IITA-Proyectos/RoboCupJunior-Soccer-Open-League-2025/Diseño3D/Grand Jaagub-Bigery.stl

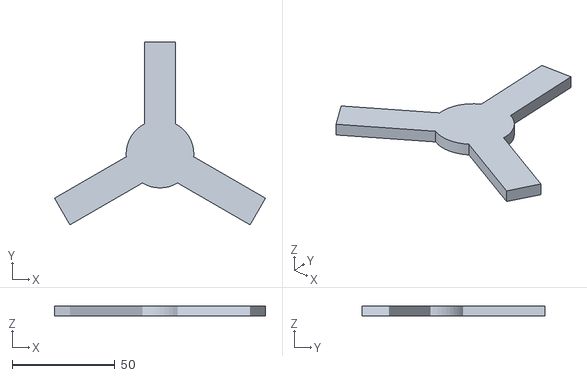
[picture p15: CAD file, 2025-07-25]
Diseño3D/Grand Jaagub-Bigery.stl
102.8 x 89.0 x 5.00
