IITA-Proyectos/RoboCupJunior-Soccer-Open-League-2025/Diseño3D/soporte TT motor_recortado 2025-07-23 - seba.stl

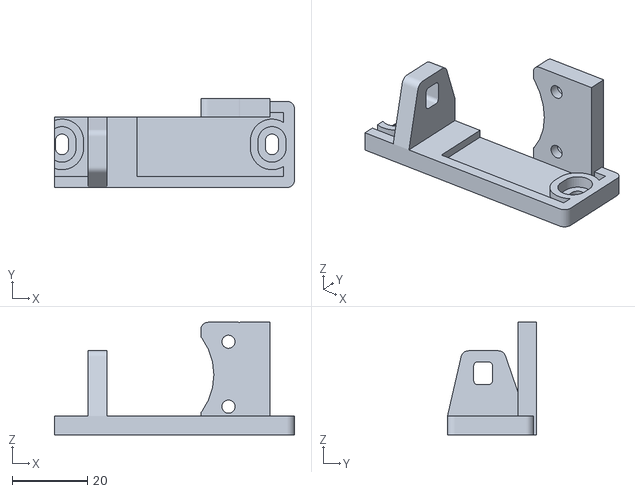
[picture p16: CAD file, 2025-07-24]
Diseño3D/soporte TT motor_recortado 2025-07-23 - seba.stl
64.0 x 23.8 x 30.0
