IITA-Proyectos/RoboCupJunior-Soccer-Open-League-2025/Diseño3D/2.0intentoconalturamijae3l.stl

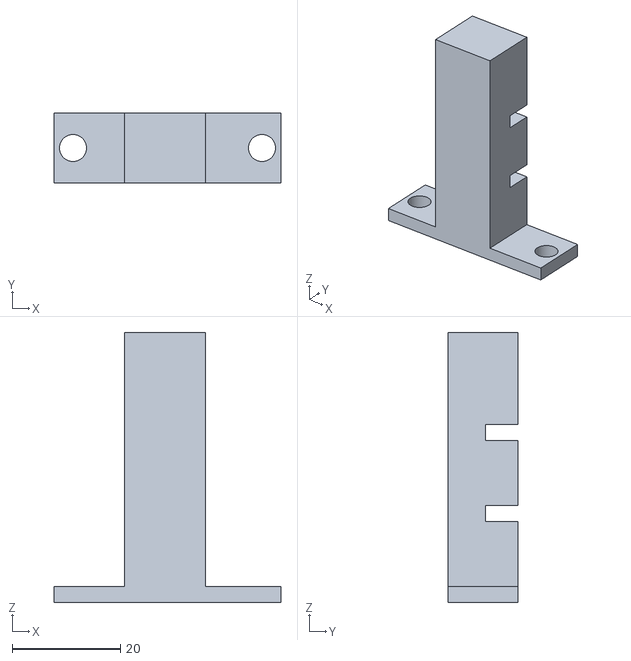
[picture p17: CAD file, 2025-07-22]
Diseño3D/2.0intentoconalturamijae3l.stl
42.0 x 13.0 x 50.0
