IITA-Proyectos/RoboCupJunior-Soccer-Open-League-2025/Diseño3D/mijael.barra.stl

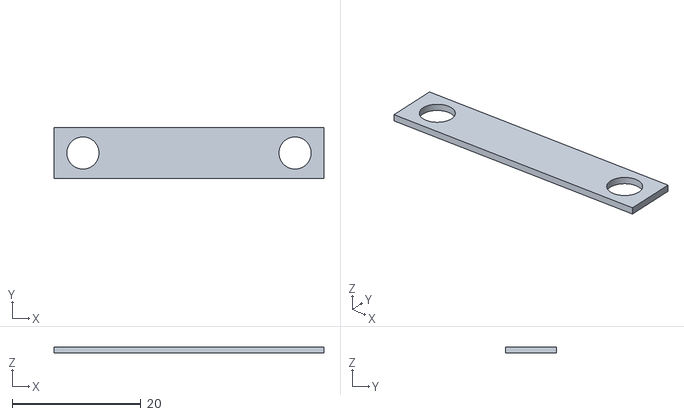
[picture p18: CAD file, 2025-07-22]
Diseño3D/mijael.barra.stl
42.0 x 8.00 x 1.00
