IITA-Proyectos/RoboCupJunior-Soccer-Open-League-2025/Diseño3D/Fabulous Lappi.stl

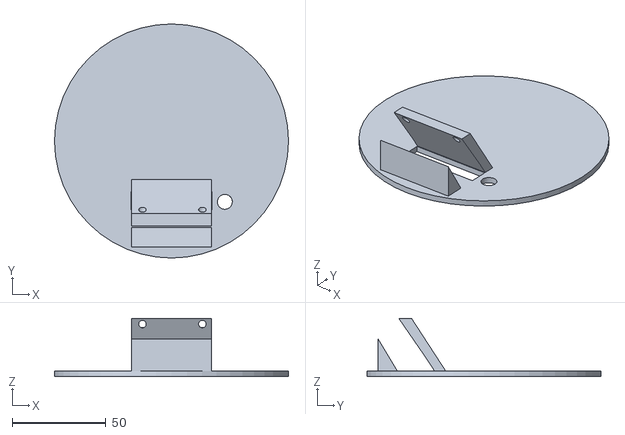
[picture p19: CAD file, 2025-07-22]
Diseño3D/Fabulous Lappi.stl
125.0 x 125.0 x 31.0
