IITA-Proyectos/RoboCupJunior-Soccer-Open-League-2025/Diseño3D/base-0.3demijael.stl

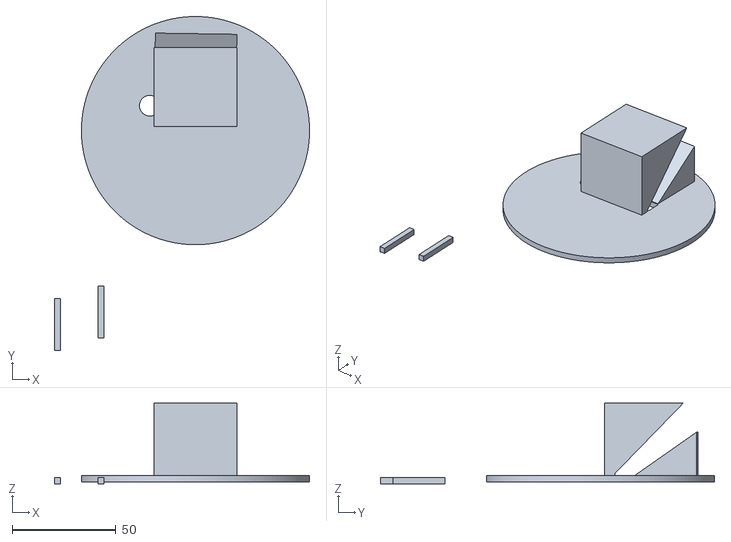
[picture p20: CAD file, 2025-07-01]
Diseño3D/base-0.3demijael.stl
123.0 x 161.0 x 39.0
