IITA-Proyectos/RoboCupJunior-Soccer-Open-League-2025/Diseño3D/Ya-lo-toque-jaja.stl

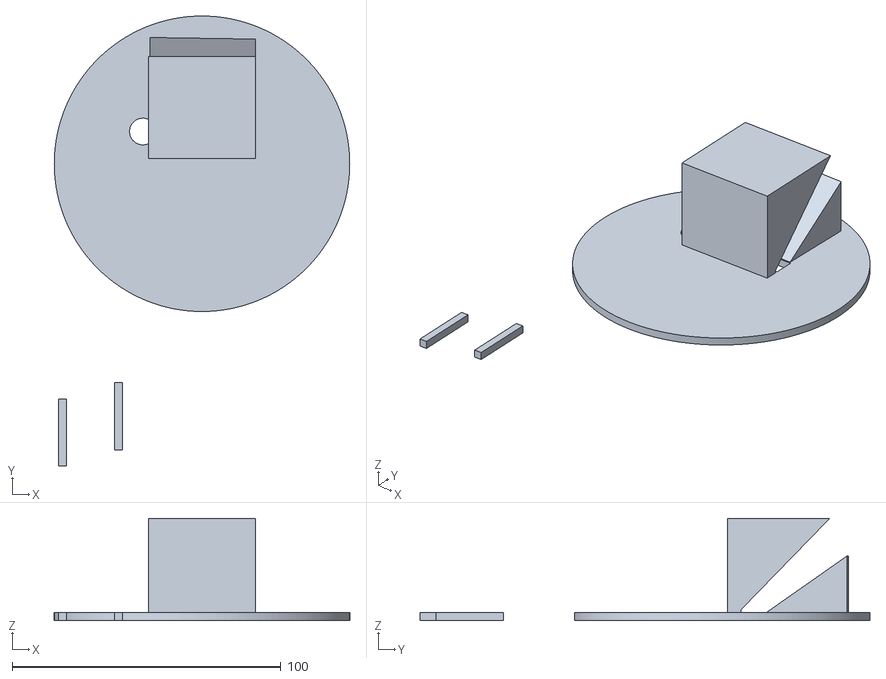
[picture p21: CAD file, 2025-06-26]
Diseño3D/Ya-lo-toque-jaja.stl
110.0 x 167.5 x 38.0
