IITA-Proyectos/RoboCupJunior-Soccer-Open-League-2025/Diseño3D/estructura para los pisos.stl

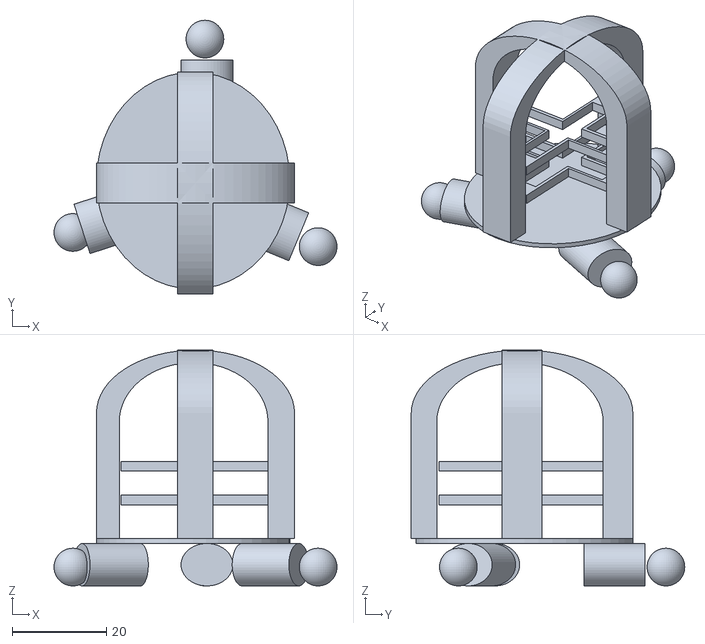
[picture p22: CAD file, 2025-06-24]
Diseño3D/estructura para los pisos.stl
60.0 x 58.0 x 50.0
