IITA-Proyectos/RoboCupJunior-Soccer-Open-League-2025/Diseño3D/Cilindro (normal).stl

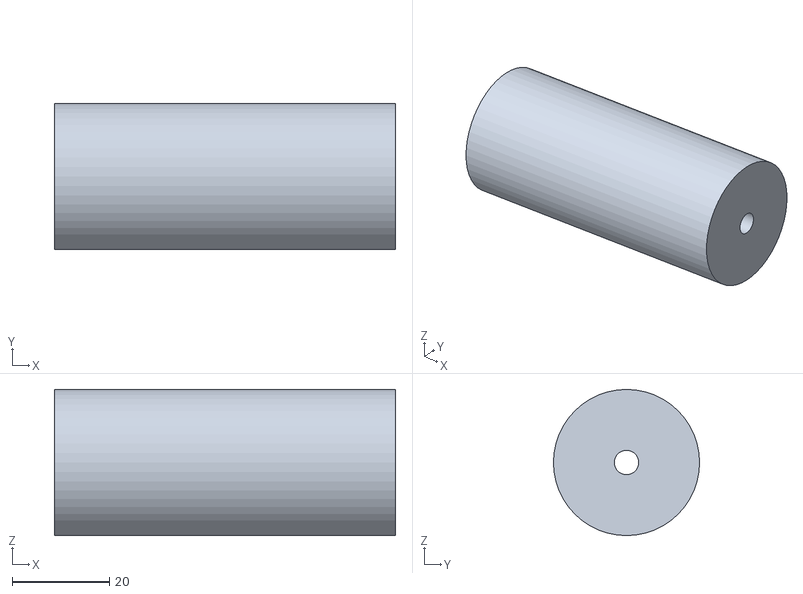
[picture p23: CAD file, 2025-06-24]
Diseño3D/Cilindro (normal).stl
70.0 x 30.0 x 30.0
