IITA-Proyectos/RoboCupJunior-Soccer-Open-League-2025/Diseño3D/Neat Stantia-Duup.stl

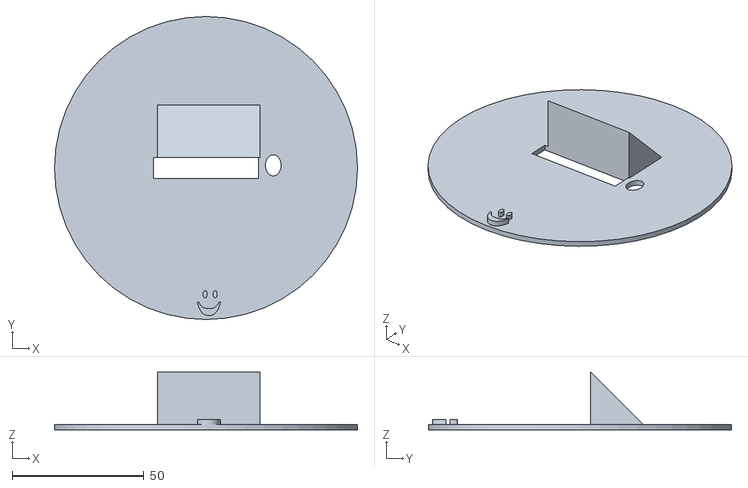
[picture p24: CAD file, 2025-06-10]
Diseño3D/Neat Stantia-Duup.stl
115.0 x 115.0 x 22.0
