IITA-Proyectos/RoboCupJunior-Soccer-Open-League-2025/Diseño3D/Dual_Servo_Bracket.stl

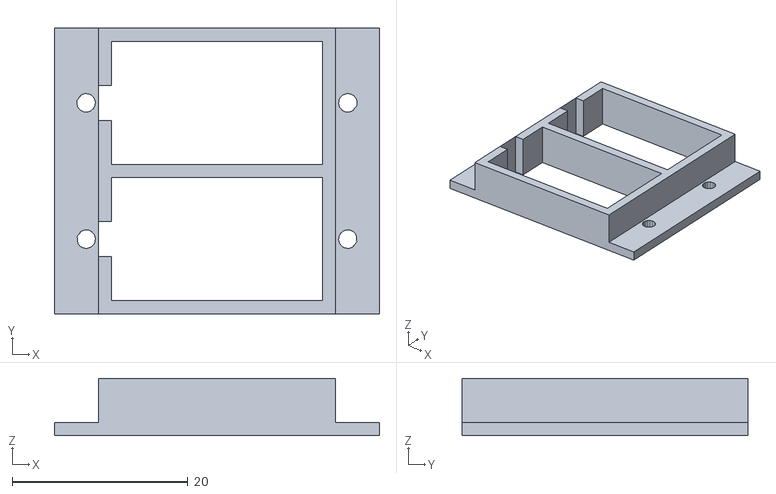
[picture p25: CAD file, 2025-06-10]
Diseño3D/Dual_Servo_Bracket.stl
37.0 x 32.5 x 6.50
