IITA-Proyectos/RoboCupJunior-Soccer-Open-League-2025/Diseño3D/Terrific Albar-Bruticus (3).stl

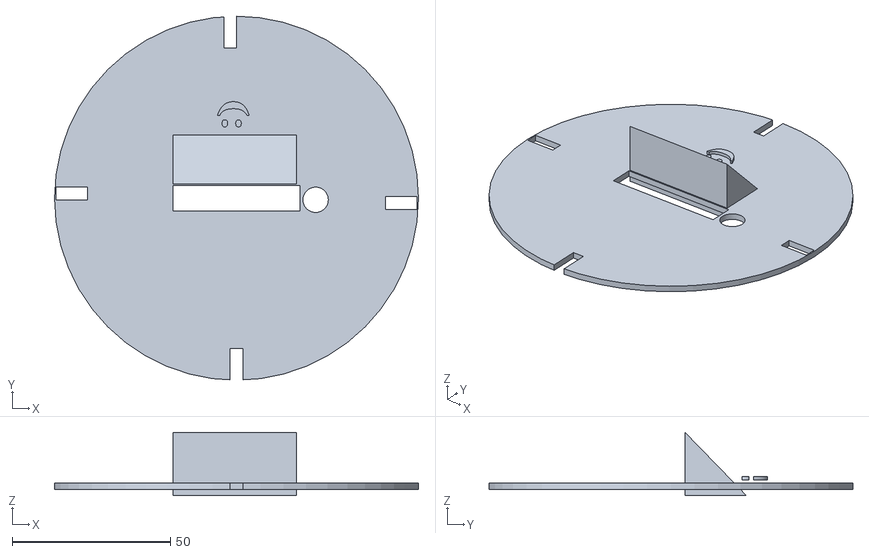
[picture p26: CAD file, 2025-06-10]
Diseño3D/Terrific Albar-Bruticus (3).stl
115.0 x 114.9 x 20.0
