IITA-Proyectos/RoboCupJunior-Soccer-Open-League-2025/Diseño3D/Daring Hango-Fyyran (1).stl

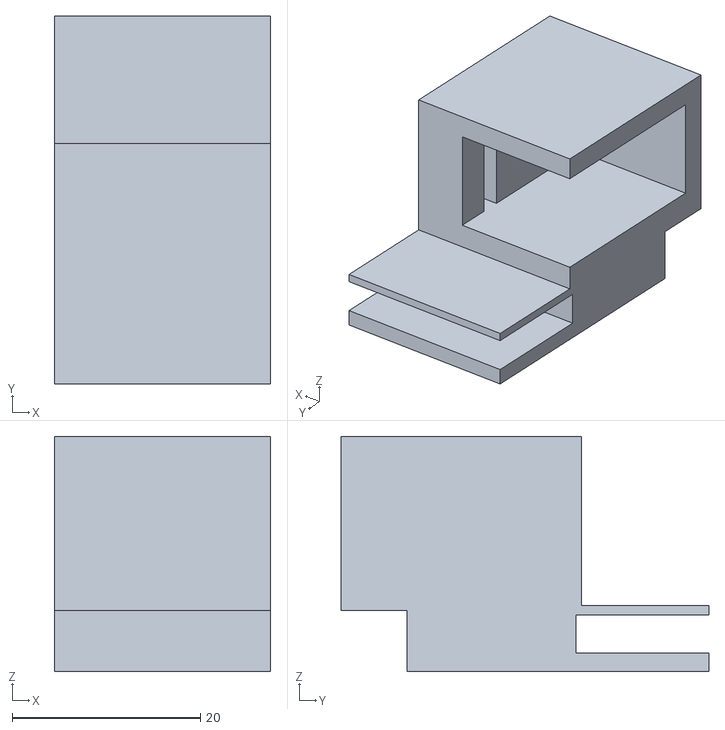
[picture p27: CAD file, 2025-06-10]
Diseño3D/Daring Hango-Fyyran (1).stl
23.0 x 39.1 x 25.0
