IITA-Proyectos/RoboCupJunior-Soccer-Open-League-2025/Diseño3D/Smashing Jofo.stl

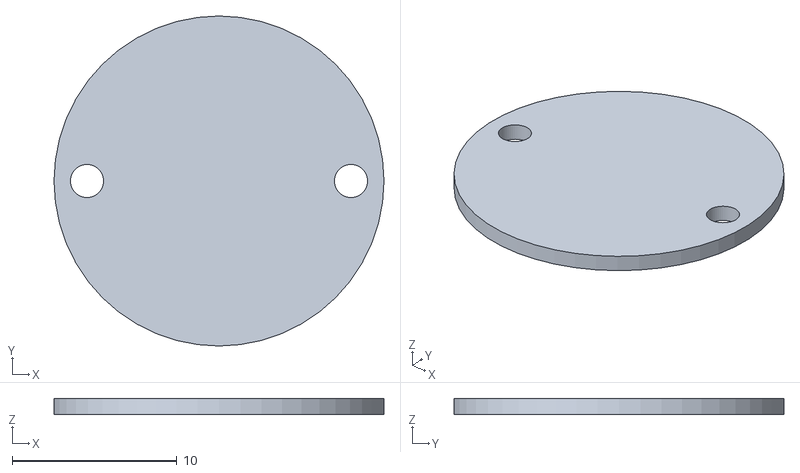
[picture p28: CAD file, 2025-06-04]
Diseño3D/Smashing Jofo.stl
20.0 x 20.0 x 1.00
