IITA-Proyectos/RoboCupJunior-Soccer-Open-League-2025/movilidad/prueba-giroscopo.ino

#include <Wire.h>
#include <Adafruit_Sensor.h>
#include <Adafruit_BNO055.h>
#include <utility/imumaths.h>
  
Adafruit_BNO055 bno = Adafruit_BNO055(55);

void setup(void) 
{
  Serial.begin(9600);
  Serial.println("Orientation Sensor Test"); Serial.println("");
  
  /* Initialise the sensor */
  if(!bno.begin())
  {
    /* There was a problem detecting the BNO055 ... check your connections */
    Serial.print("Ooops, no BNO055 detected ... Check your wiring or I2C ADDR!");
    while(1);
  }
  
  delay(1000);
    
  bno.setExtCrystalUse(true);
}

void loop(void) 
{
  /* Get a new sensor event */ 
  sensors_event_t event; 
 imu::Vector<3> euler = bno.getVector(Adafruit_BNO055::VECTOR_EULER);
  
/* Display the floating point data */
Serial.print("X: ");
Serial.print(euler.x());
Serial.print(" Y: ");
Serial.print(euler.y());
Serial.print(" Z: ");
Serial.print(euler.z());
Serial.println("");
  delay(100);
}
